wintercharm/Winter-One/Winter One STEP v13/v12 Foot.STEP

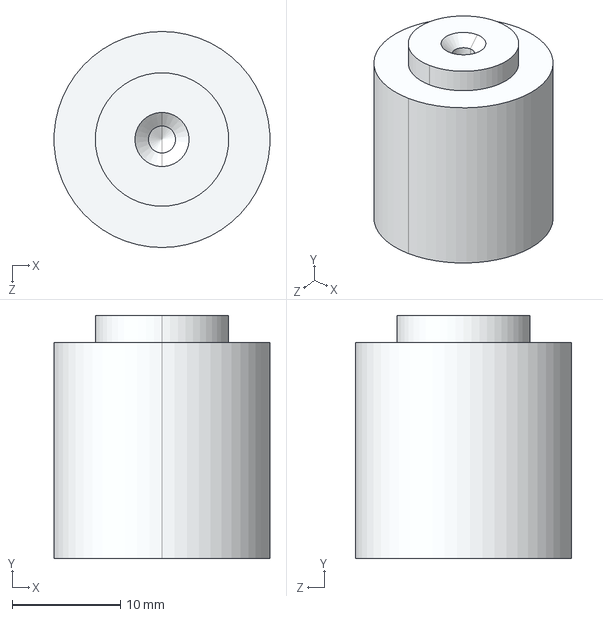
[picture p15: CAD file, 2023-03-20]
Winter One STEP v13/v12 Foot.STEP
20.0 x 22.5 x 20.0 mm
