wintercharm/Winter-One/Winter One STEP v13/v13 PCIE Cover.STEP

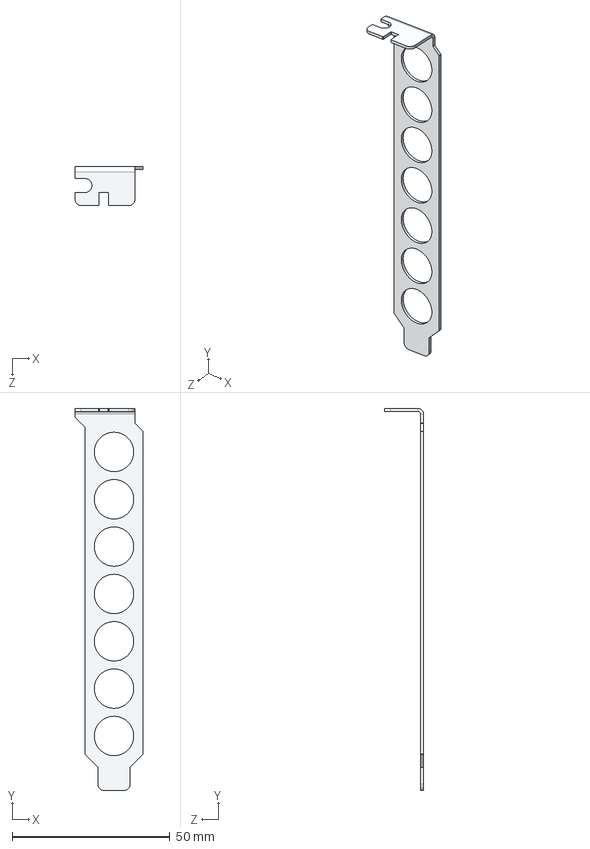
[picture p16: CAD file, 2023-03-20]
Winter One STEP v13/v13 PCIE Cover.STEP
21.6 x 121.0 x 12.4 mm
