wintercharm/Winter-One/Winter One STEP v13/v13 Drive Cage Upper.STEP

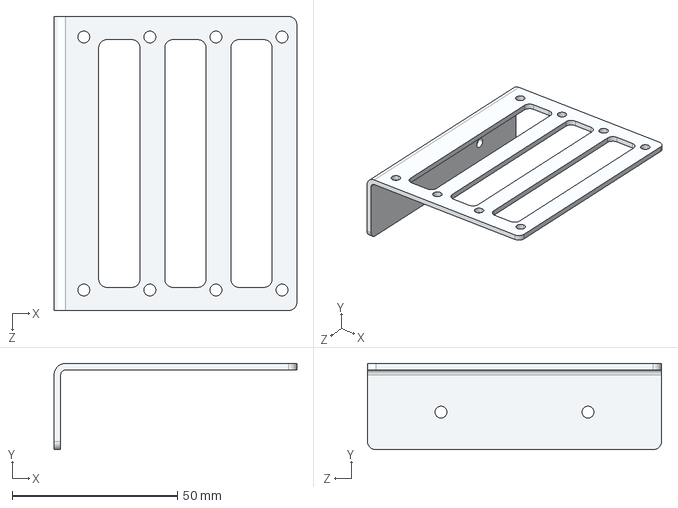
[picture p17: CAD file, 2023-03-20]
Winter One STEP v13/v13 Drive Cage Upper.STEP
73.5 x 26.1 x 89.0 mm
