wintercharm/Winter-One/Winter One STEP v13/v13 Side Panel Window.STEP

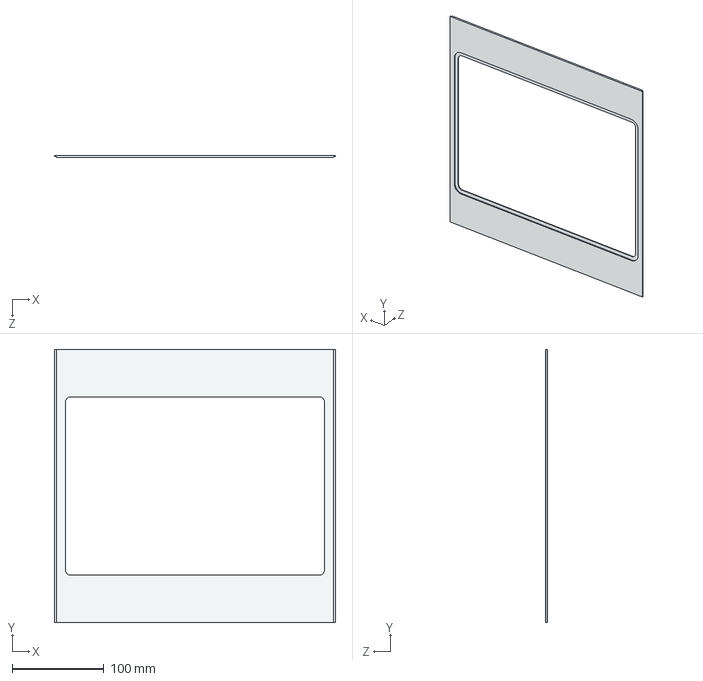
[picture p18: CAD file, 2023-03-20]
Winter One STEP v13/v13 Side Panel Window.STEP
306.2 x 297.5 x 2.50 mm
