wintercharm/Winter-One/Winter One STEP v13/v12 PSU Bracket.STEP

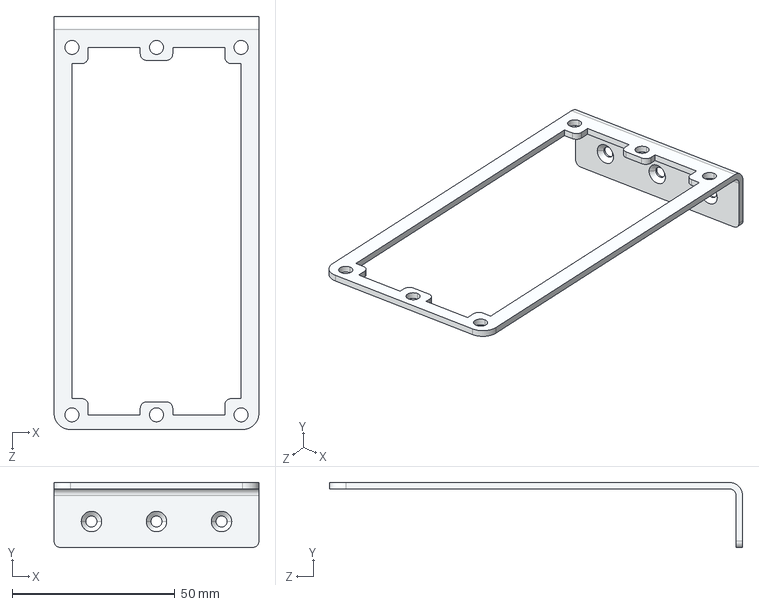
[picture p19: CAD file, 2023-03-20]
Winter One STEP v13/v12 PSU Bracket.STEP
63.0 x 20.0 x 127.0 mm
